SebastianZientek/Humi/src/App.hpp

#pragma once

#include <Arduino.h>
#include <LittleFS.h>

#include <memory>
#include <nlohmann/json.hpp>

#include "ArduinoDevice.hpp"
#include "Configuration.hpp"
#include "HumidifierUart.hpp"
#include "MessageEncoder.hpp"
#include "MqttAdp.hpp"
#include "MqttHumidifier.hpp"
#include "Resources.hpp"
#include "Timer.hpp"
#include "WebPage.hpp"
#include "WebServer/EventSrcClient.hpp"
#include "WebServer/WebRequest.hpp"
#include "WebServer/WebServer.hpp"
#include "FilesystemAdp.hpp"

class App
{
public:
    void init();
    void update();

private:
    void setupPeripherals();
    void setupWifi();
    void setupWebPage();
    void setupDefaultState();
    void setupHumidifierUart();
    void setupMqtt();
    void setupTimers();

    bool isEmergencyFlashingModeAfterCrash();
    void setupEmergencyFlashingOverOTA();

    using WebSrv = WebServer<WebRequest, EventSrcClient>;
    using MainWebPage = WebPage<WebSrv, Resources>;
    constexpr static auto m_serialSpeed = 9600;

    std::shared_ptr<WebSrv> m_webSrv{std::make_shared<WebSrv>(80)};
    MainWebPage m_webPage{m_webSrv};
    HumidifierUart<decltype(Serial), MessageEncoder> m_humidifierUart{&Serial};
    nlohmann::json m_humidifierState;
    std::shared_ptr<MqttAdp> m_mqttAdp{std::make_shared<MqttAdp>()};
    std::shared_ptr<MqttHumidifier<MqttAdp>> m_mqttHumidifier;
    FilesystemAdp m_filesystem;
    Configuration<FilesystemAdp> m_config{m_filesystem};
    bool m_shouldRestart{false};

    Timer<ArduinoDevice> m_humidifierUartTimer;
    Timer<ArduinoDevice> m_otaTimer;
    Timer<ArduinoDevice> m_stateUpdateTimer;
};
